cayunus/EE464-TermProject/Cayunus/Calculations/RmsOfTrapezoid&Triangular.pdf

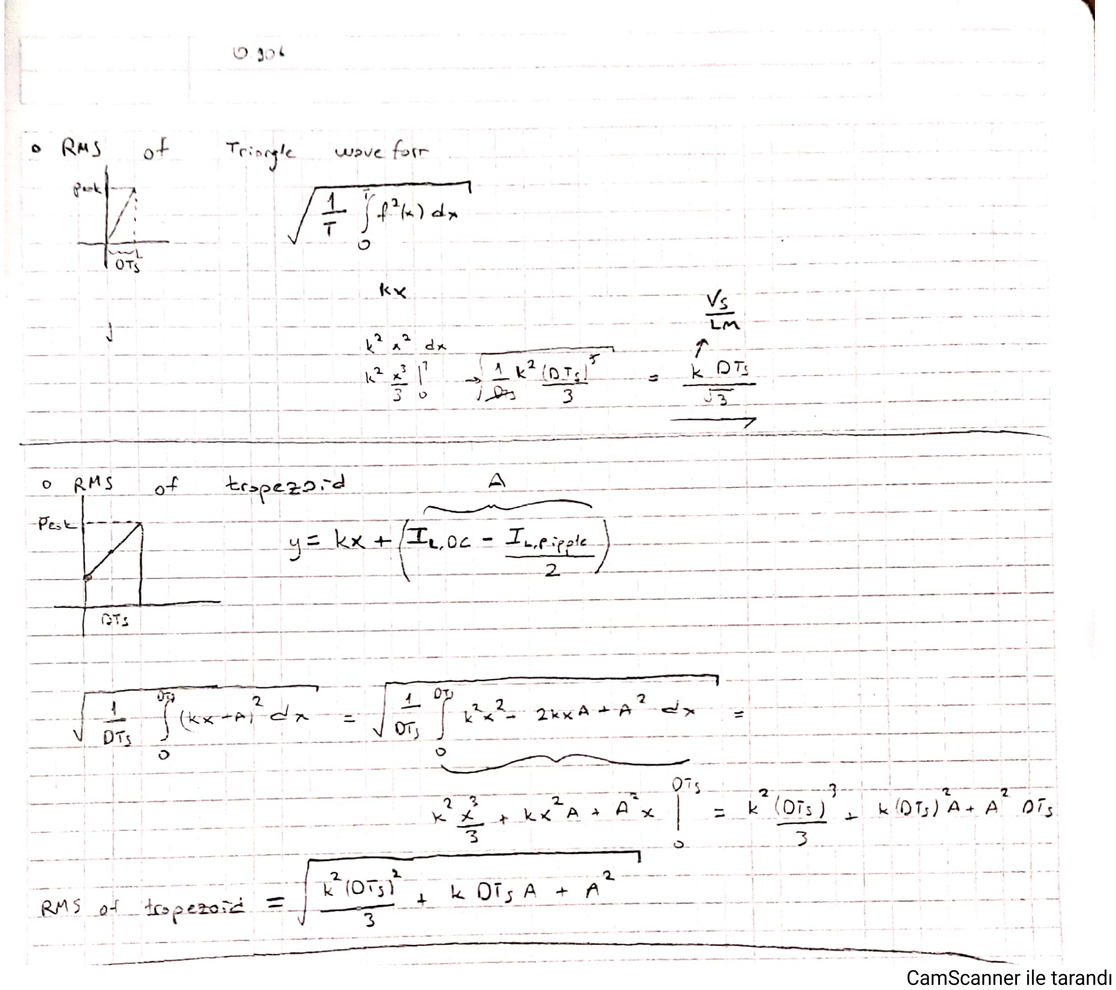
[picture p64: page 1]
