cayunus/EE464-TermProject/PCB/EE464_PCB_Yunus/Downloaded_Sym_Foot/ETD34/User Library-ETD34.STEP

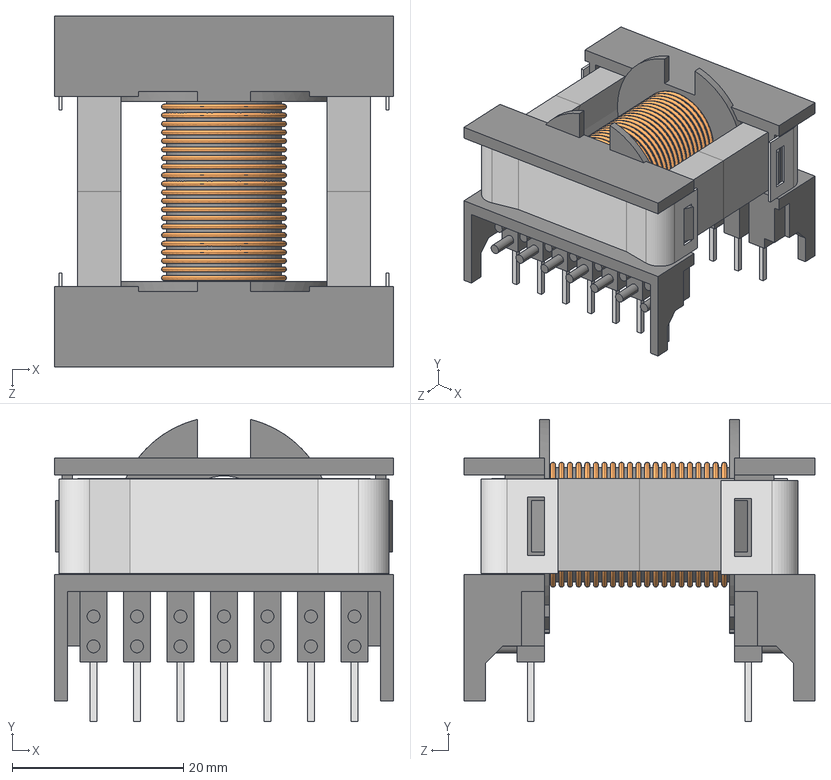
[picture p80: CAD file, 2021-06-09]
PCB/EE464_PCB_Yunus/Downloaded_Sym_Foot/ETD34/User Library-ETD34.STEP
39.6 x 35.3 x 41.0 mm
ETD34_Part3 x 2
ETD34_Part4
CPH-ETD34-1S-14P
ETD34_Part2 x 2
