cayunus/EE464-TermProject/PCB/EE464_PCB_Yunus/Downloaded_Sym_Foot/LT8316IFE_UltraLib/AltiumDesigner/2021-05-20_21-10-27/TSSOP_20_ADI.step

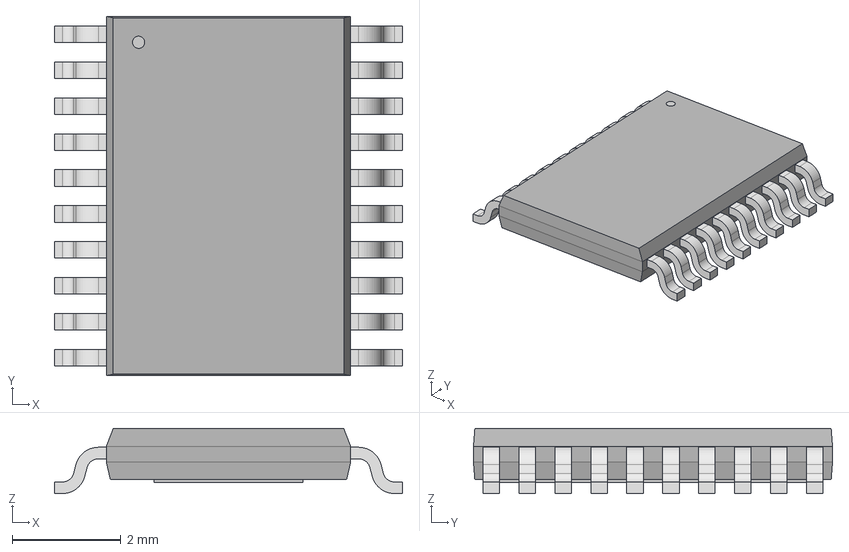
[picture p81: CAD file, 2021-05-27]
PCB/EE464_PCB_Yunus/Downloaded_Sym_Foot/LT8316IFE_UltraLib/AltiumDesigner/2021-05-20_21-10-27/TSSOP_20_ADI.step
6.40 x 6.60 x 1.20 mm
