cayunus/EE464-TermProject/PCB/EE464_PCB_Yunus/Downloaded_Sym_Foot/R0603/User Library-CR1608-0603.step

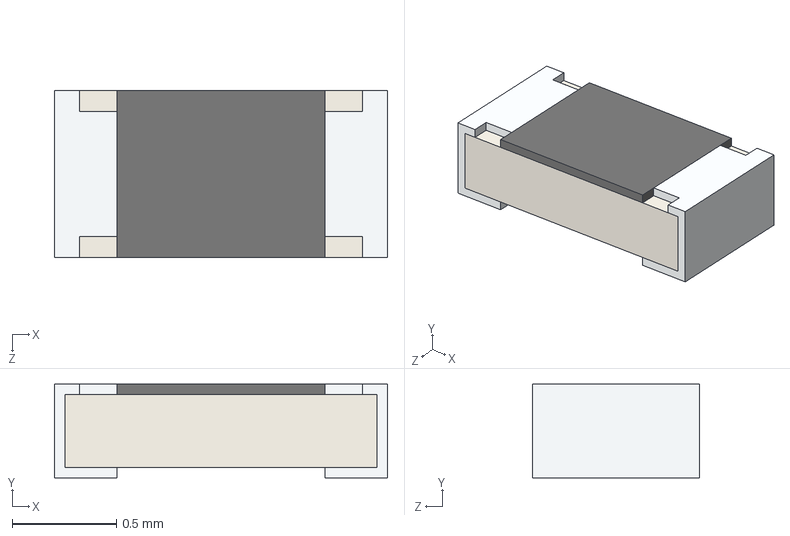
[picture p82: CAD file, 2021-05-27]
PCB/EE464_PCB_Yunus/Downloaded_Sym_Foot/R0603/User Library-CR1608-0603.step
1.60 x 0.45 x 0.8 mm
