cayunus/EE464-TermProject/PCB/EE464_PCB_Yunus/Downloaded_Sym_Foot/Rsense1220/AltiumDesigner/2021-05-21_21-18-42/RES_1220_SUS.step

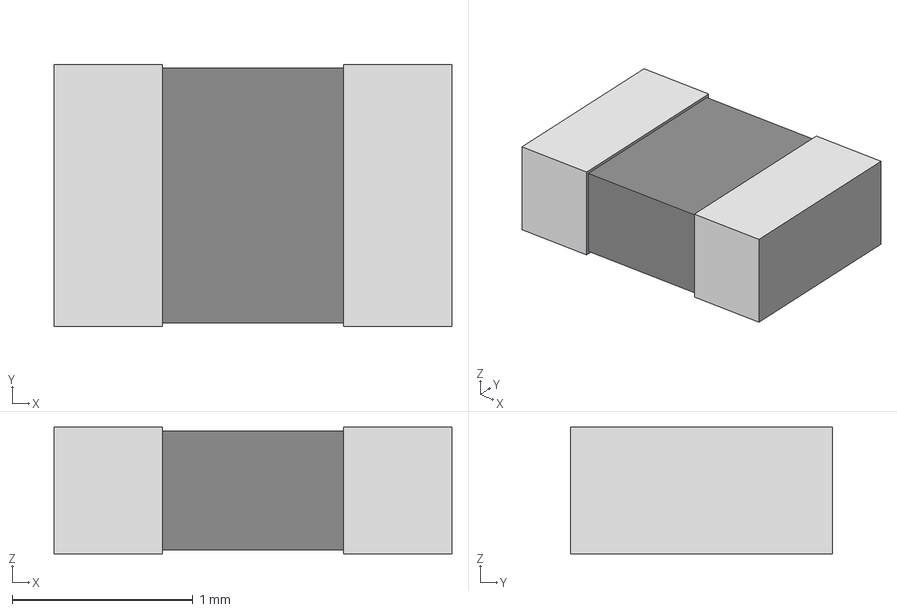
[picture p83: CAD file, 2021-05-27]
PCB/EE464_PCB_Yunus/Downloaded_Sym_Foot/Rsense1220/AltiumDesigner/2021-05-21_21-18-42/RES_1220_SUS.step
2.20 x 1.45 x 0.7 mm
