cayunus/EE464-TermProject/PCB/EE464_PCB_Yunus/Downloaded_Sym_Foot/SOD128/User Library-SOD128.step

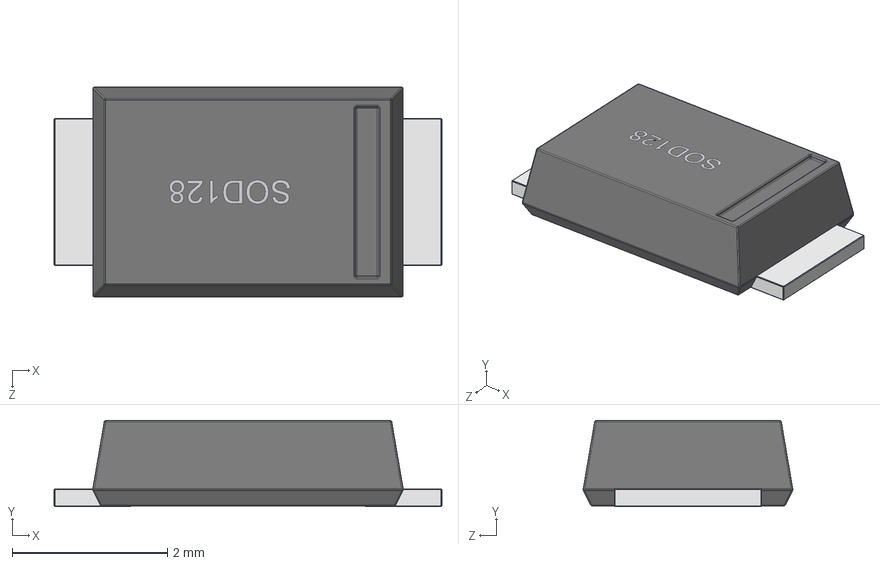
[picture p84: CAD file, 2021-06-09]
PCB/EE464_PCB_Yunus/Downloaded_Sym_Foot/SOD128/User Library-SOD128.step
5.00 x 1.11 x 2.70 mm
