cayunus/EE464-TermProject/PCB/EE464_PCB_Yunus/Downloaded_Sym_Foot/TO220-AB/stps20h100ct.stp

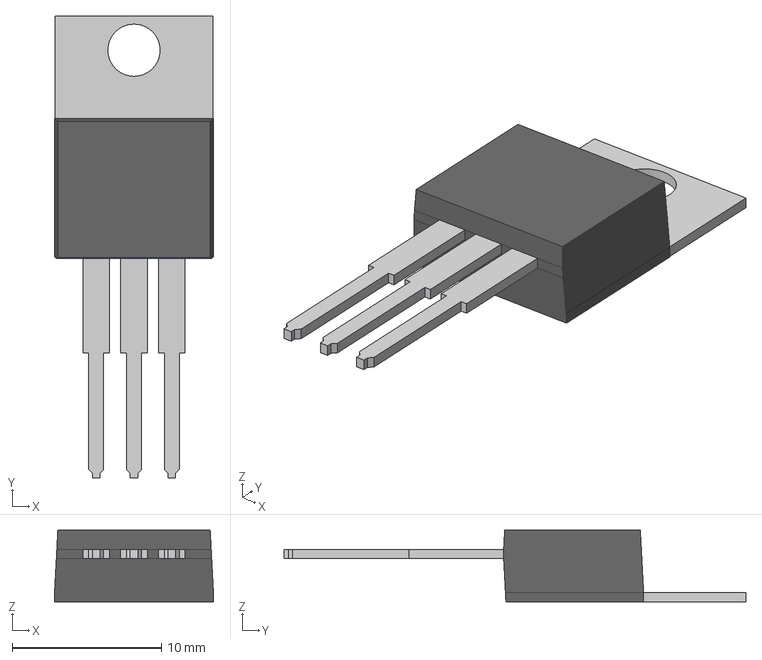
[picture p85: CAD file, 2021-06-09]
PCB/EE464_PCB_Yunus/Downloaded_Sym_Foot/TO220-AB/stps20h100ct.stp
10.7 x 31.0 x 4.83 mm
