cayunus/EE464-TermProject/PCB PDF/Flyback_PCB.pdf

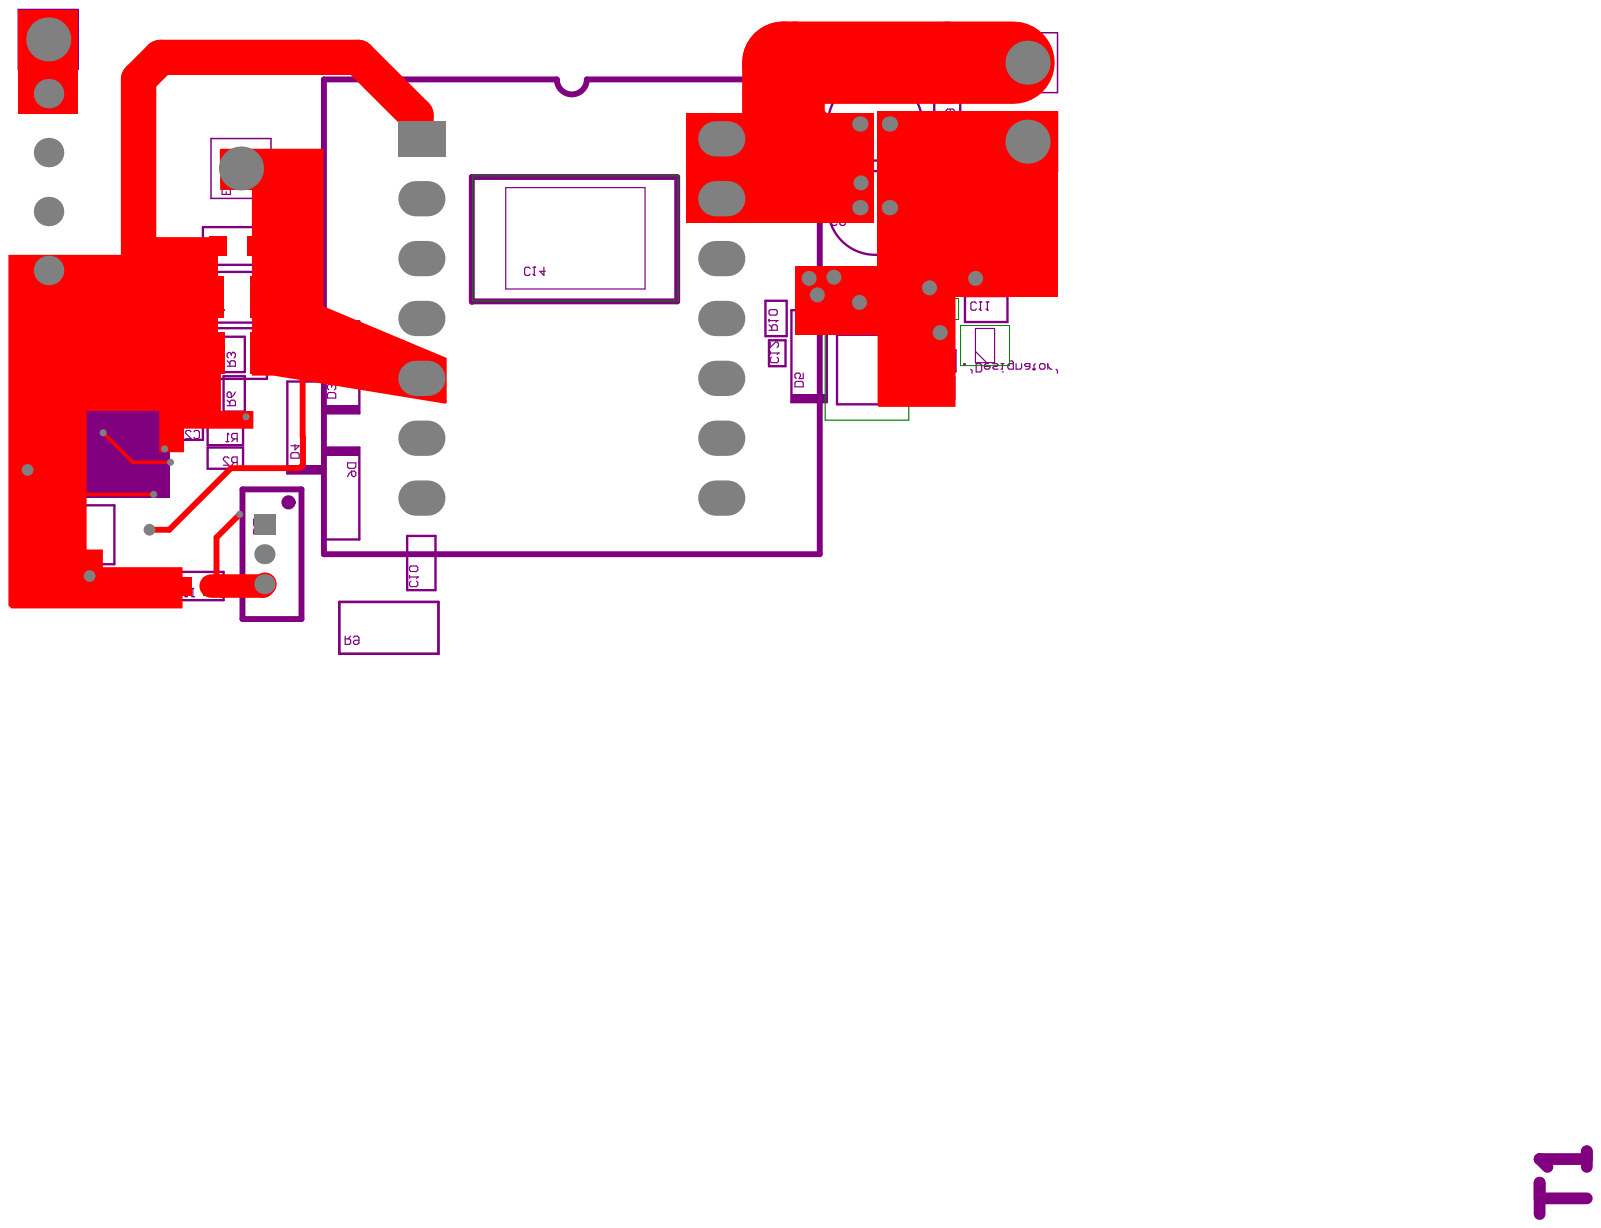
[picture p86: page 1]

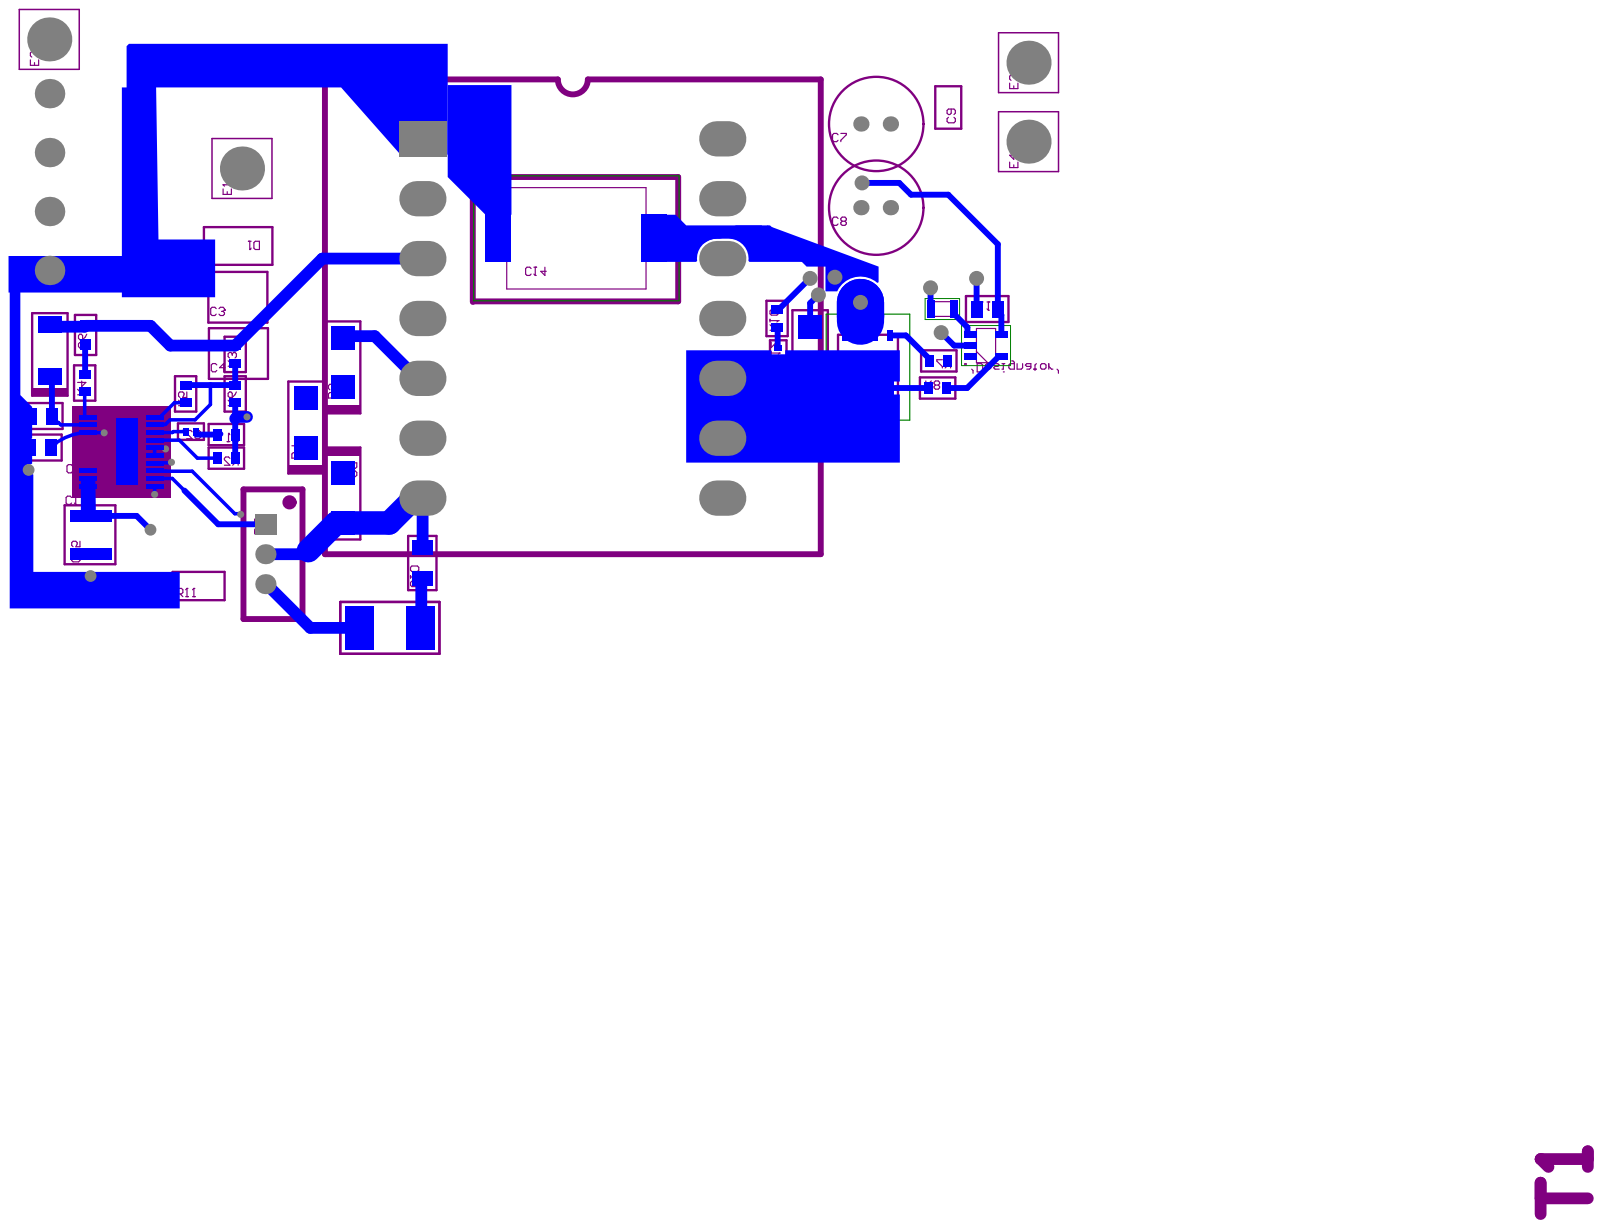
[picture p87: page 2]

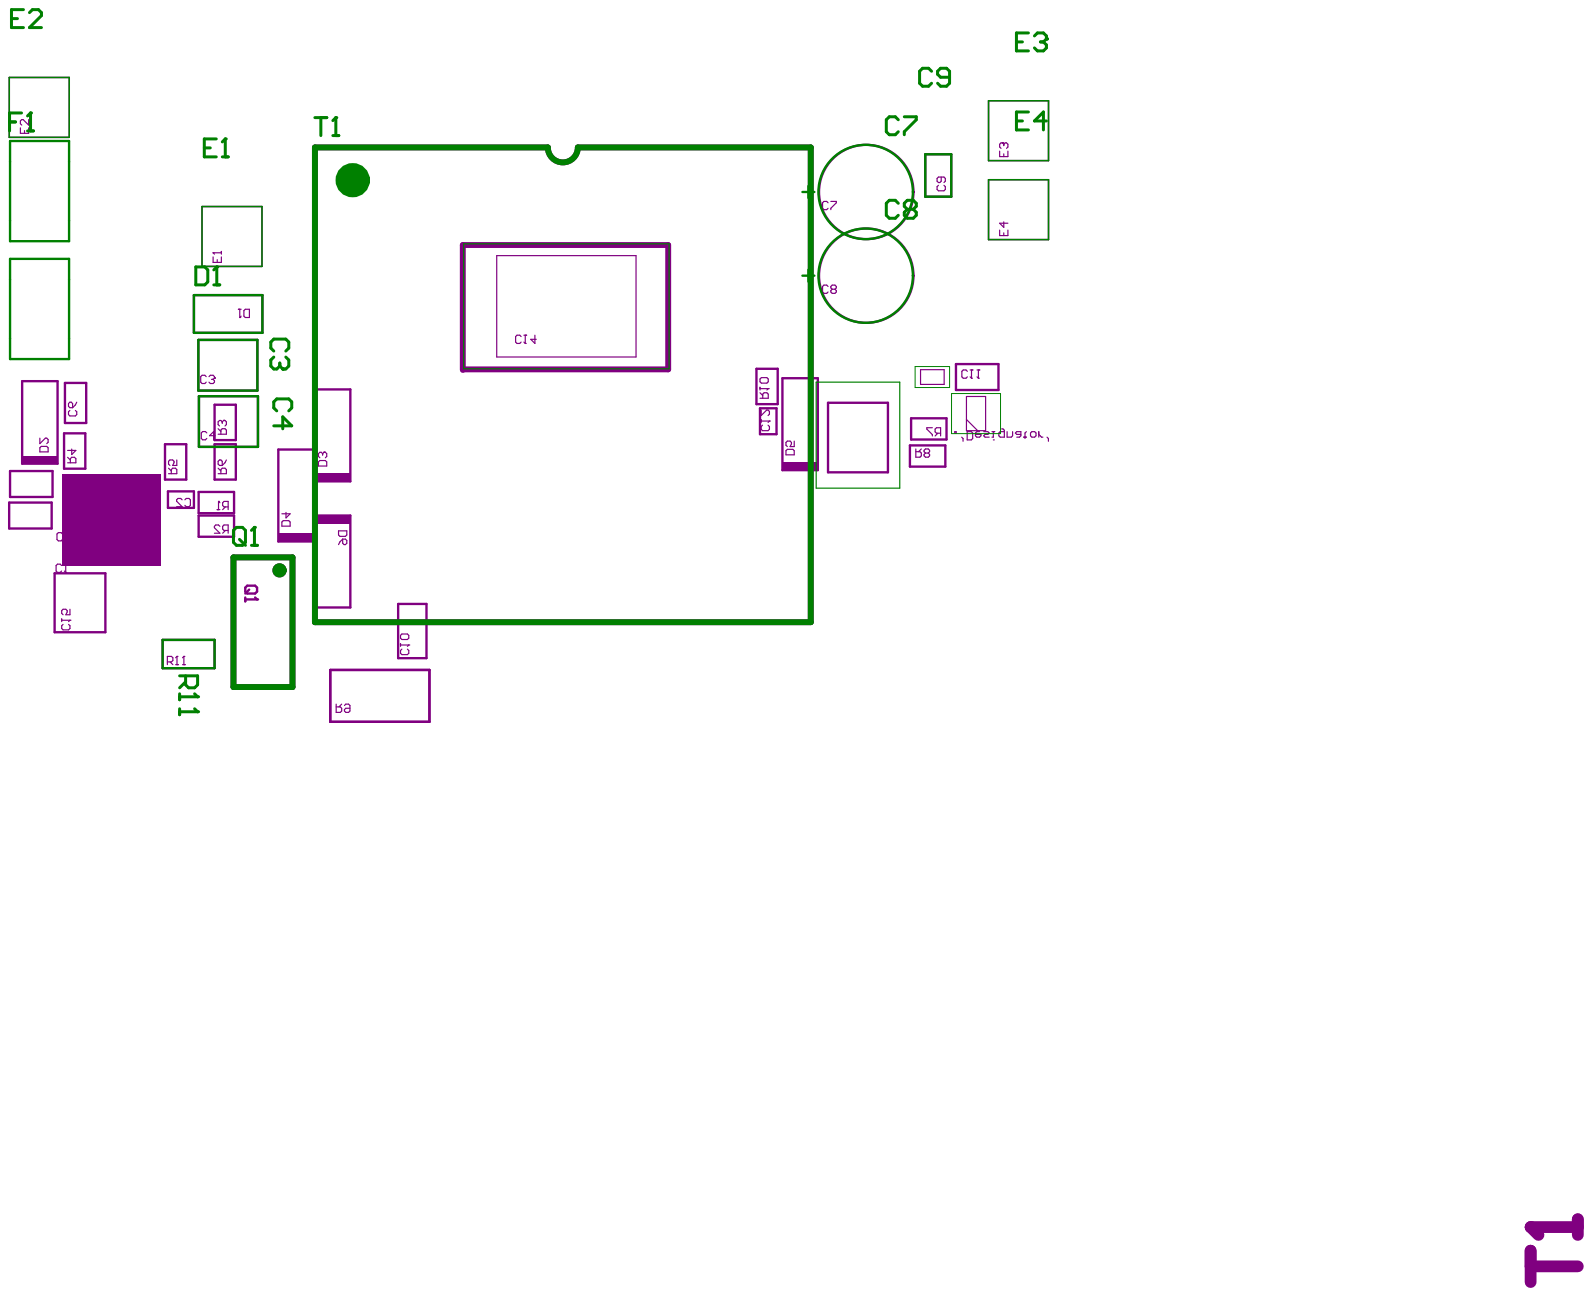
[picture p88: page 3]

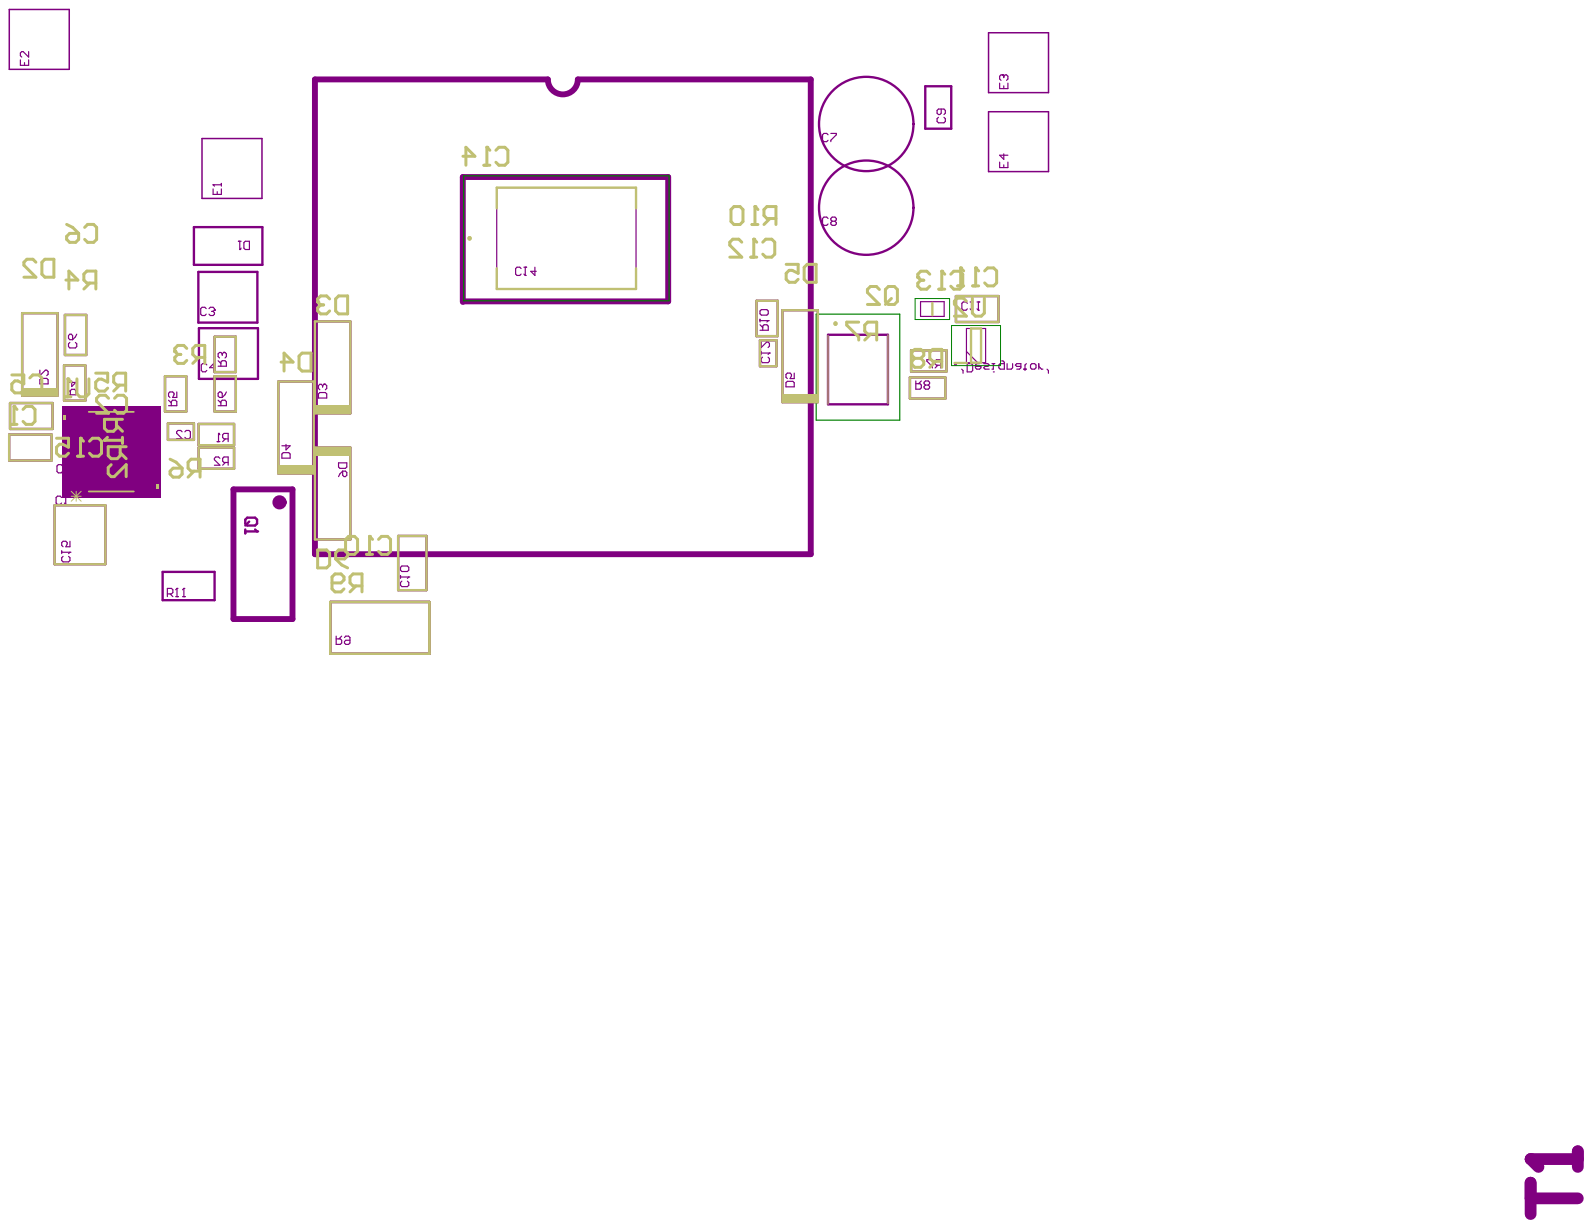
[picture p89: page 4]

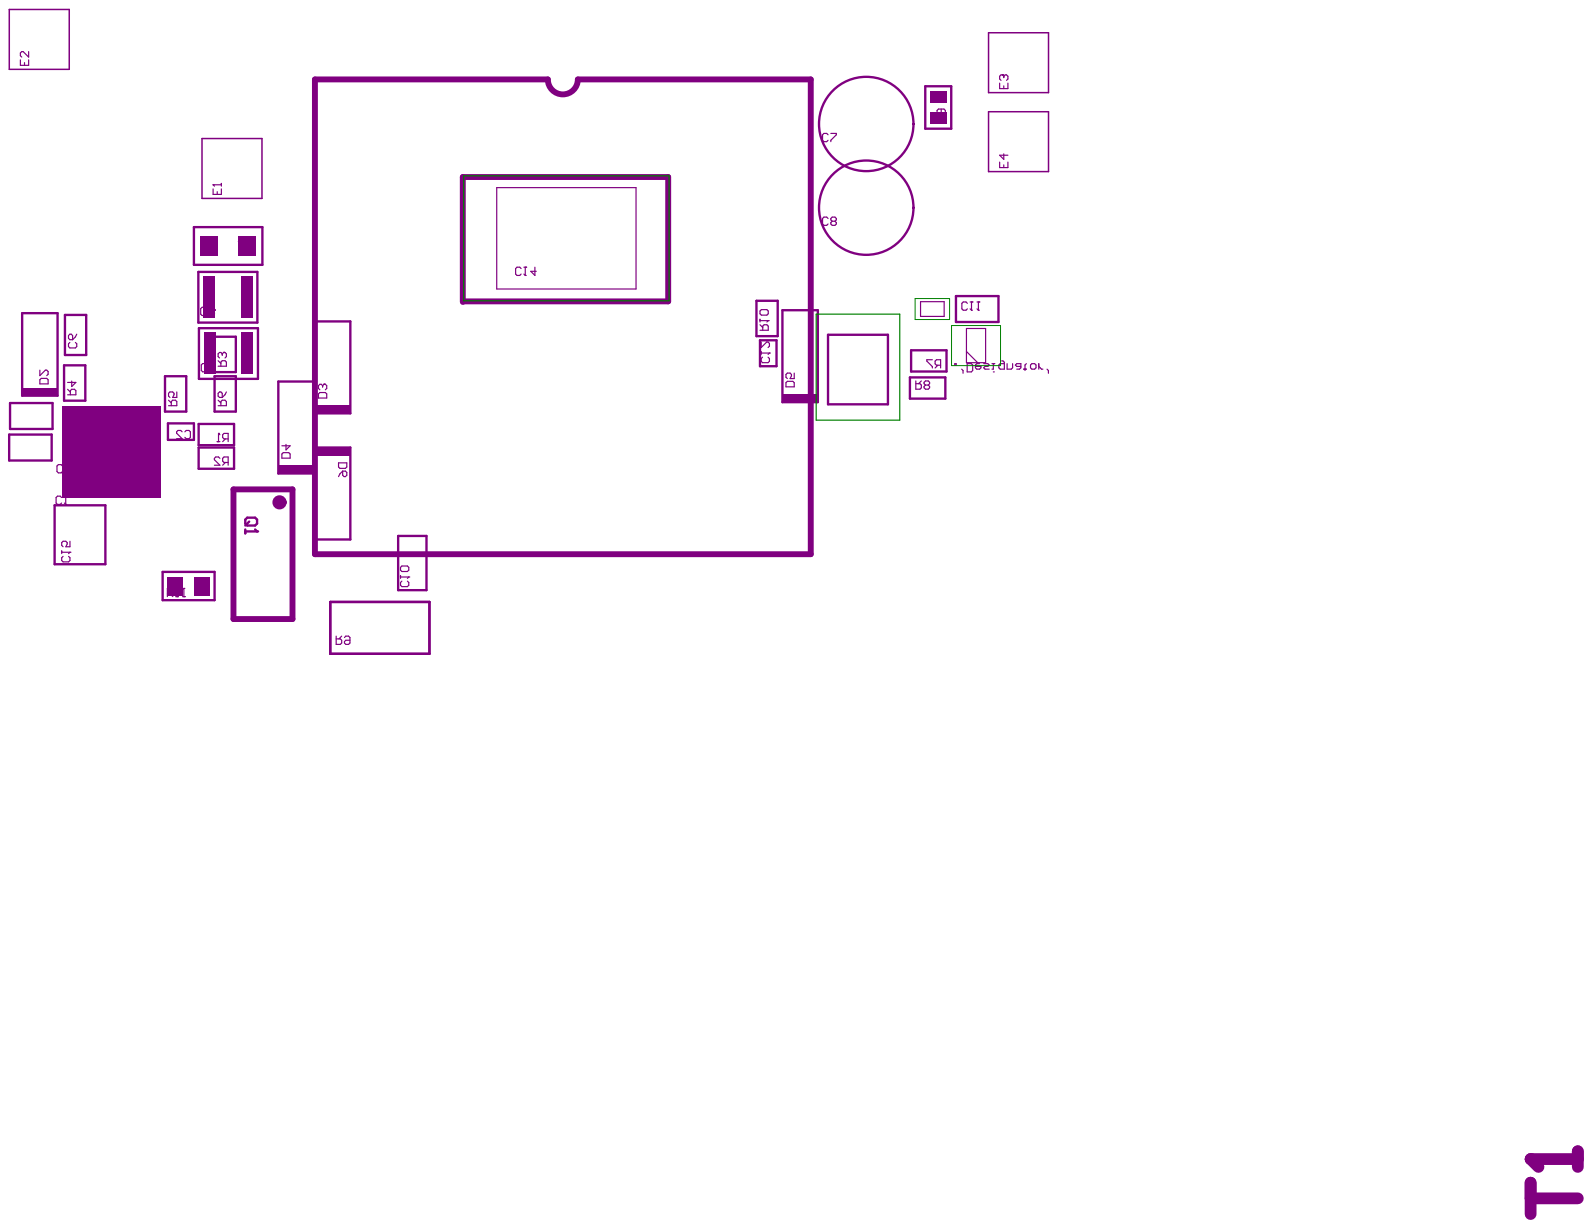
[picture p90: page 5]

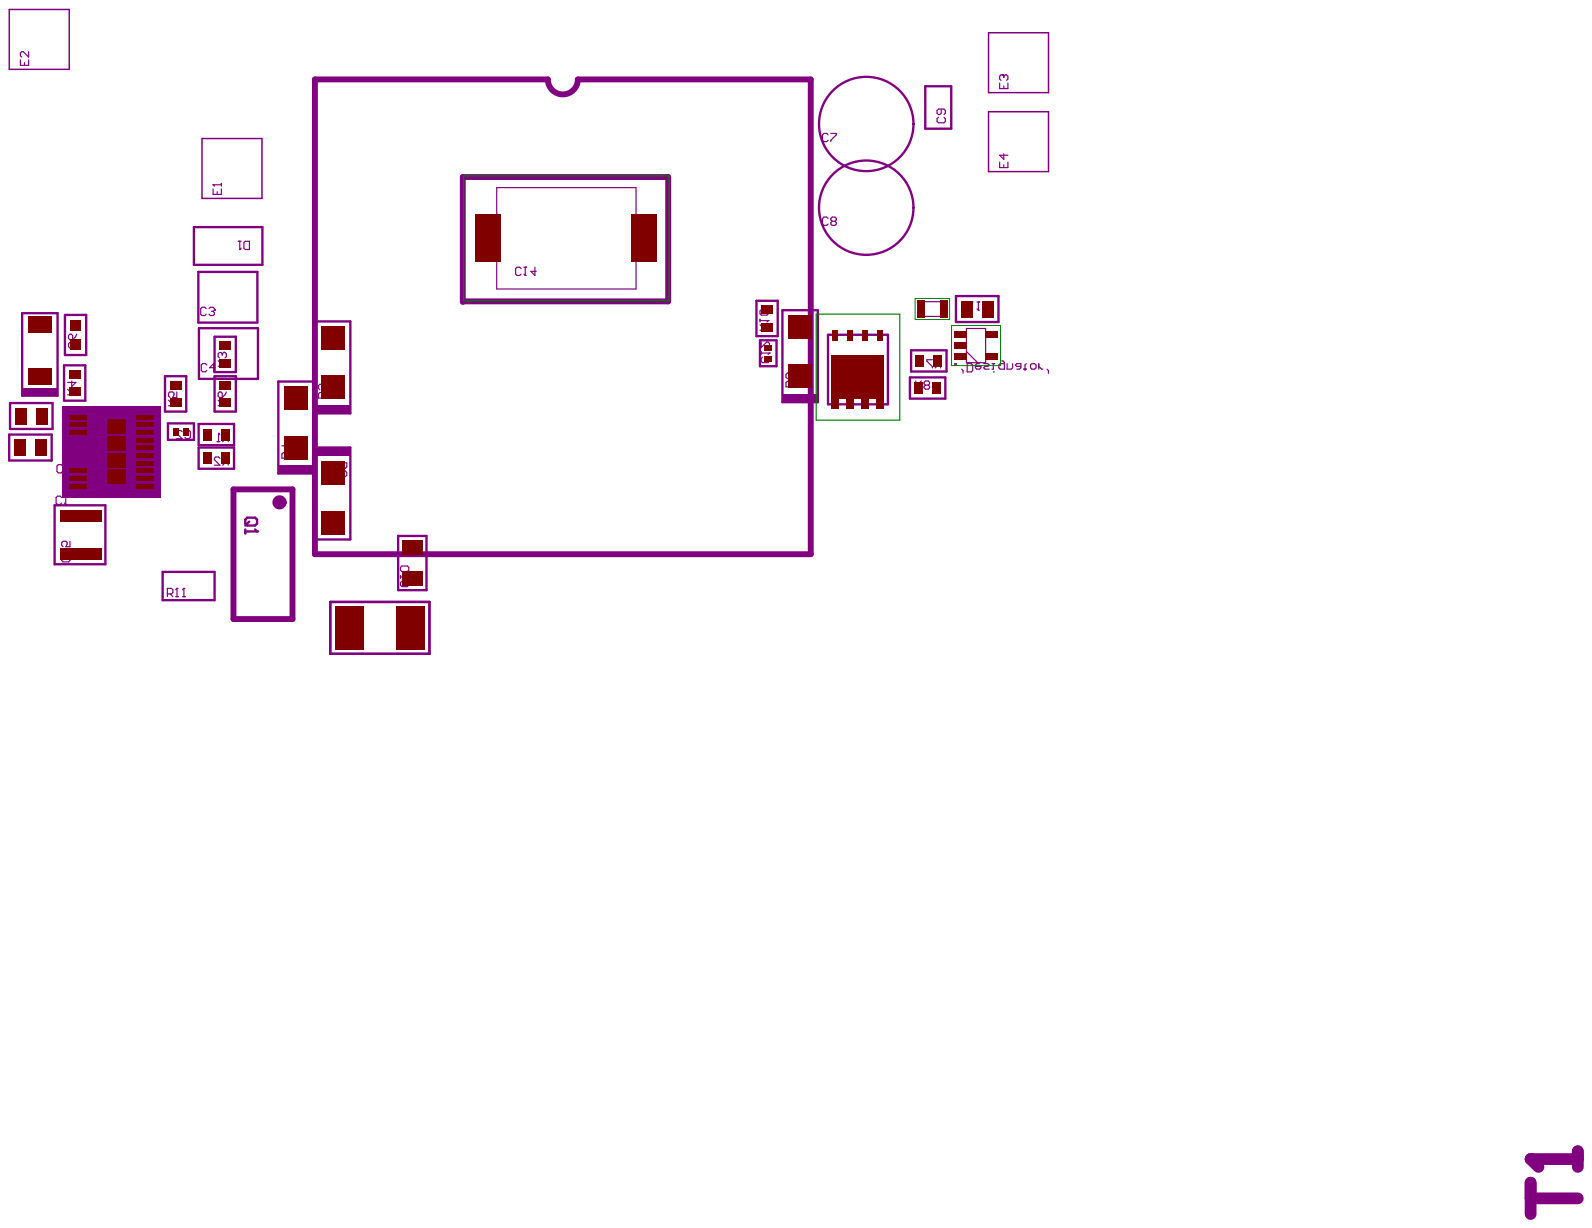
[picture p91: page 6]

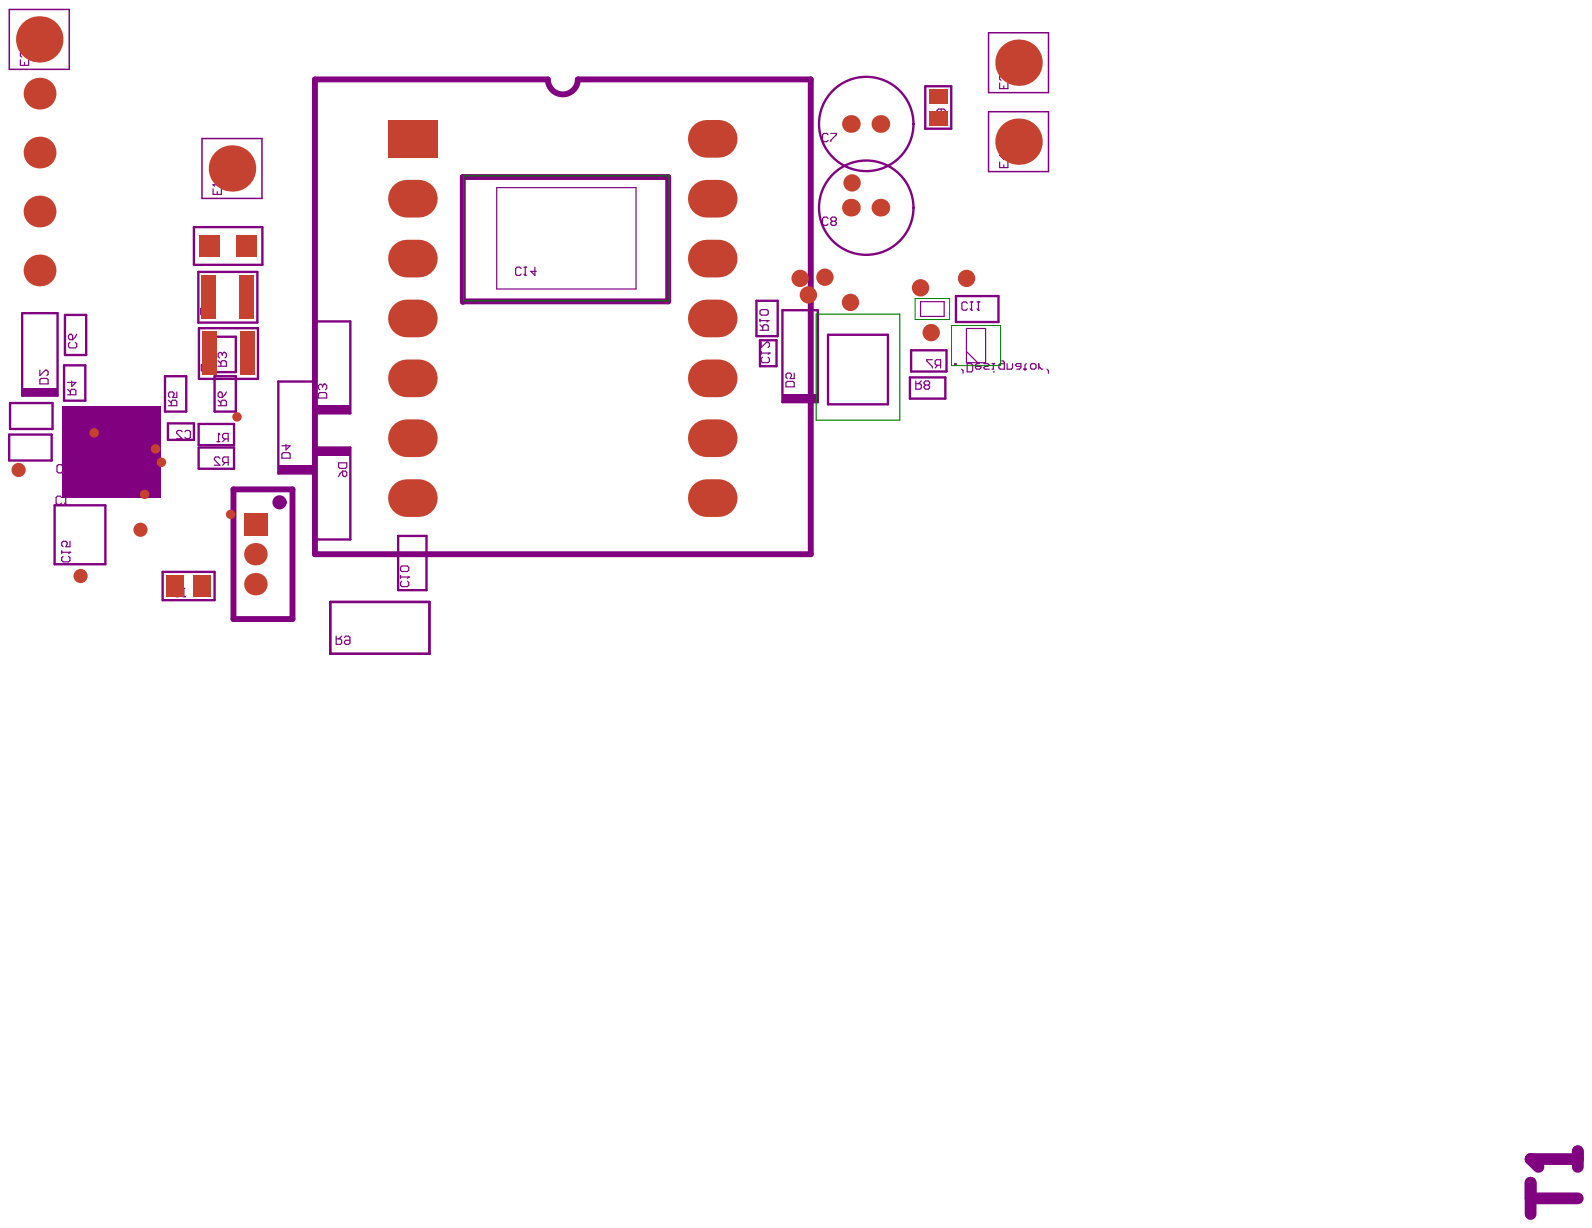
[picture p92: page 7]

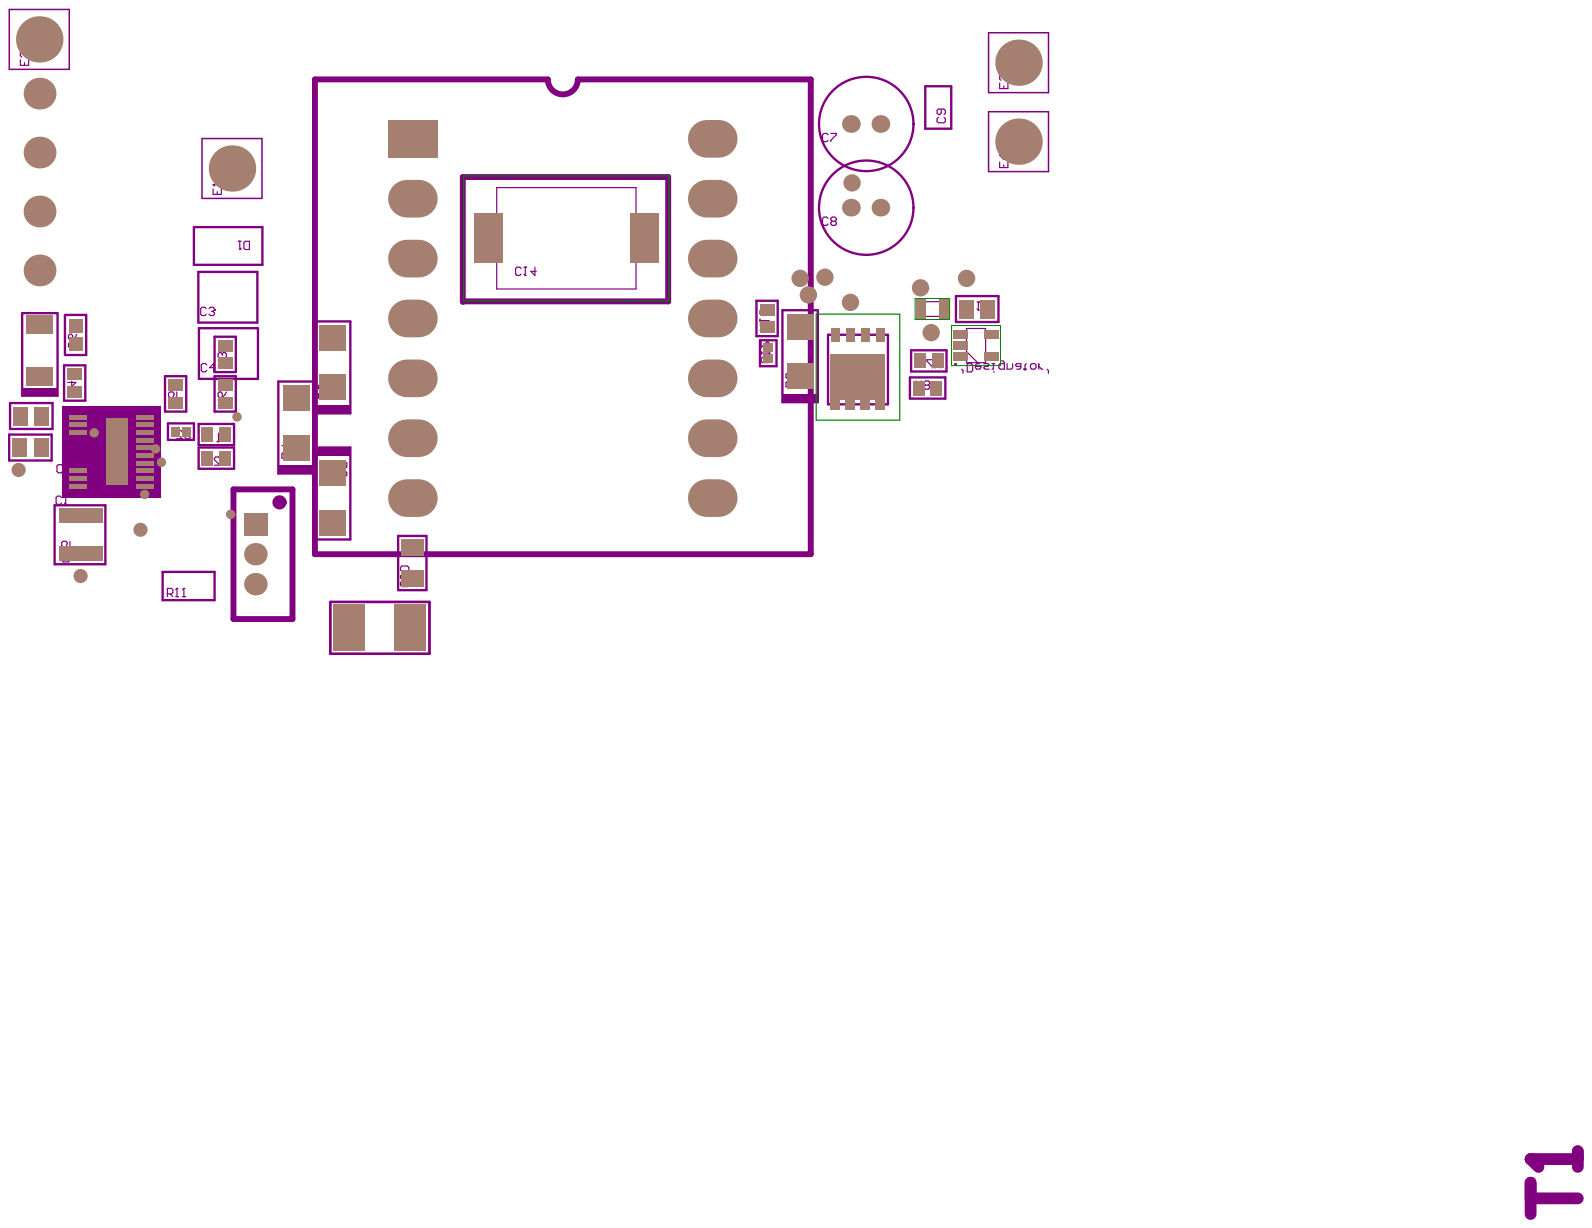
[picture p93: page 8]

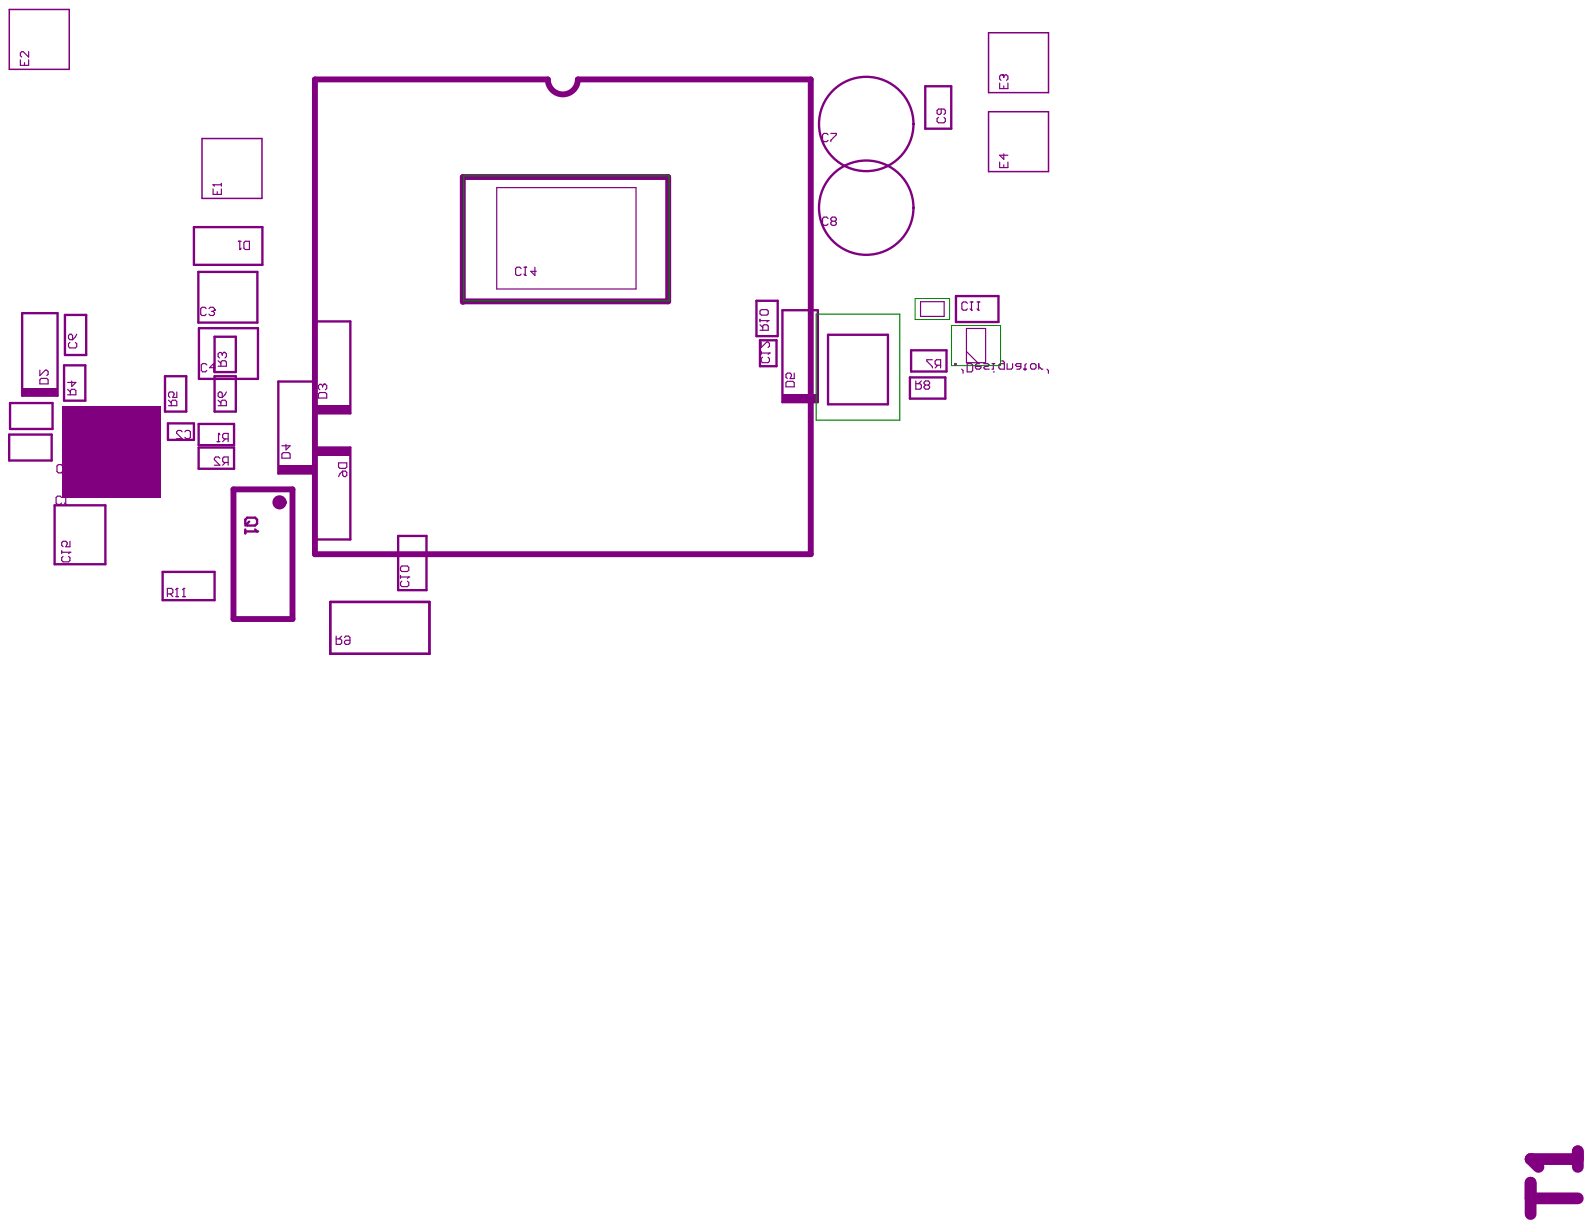
[picture p94: page 9]

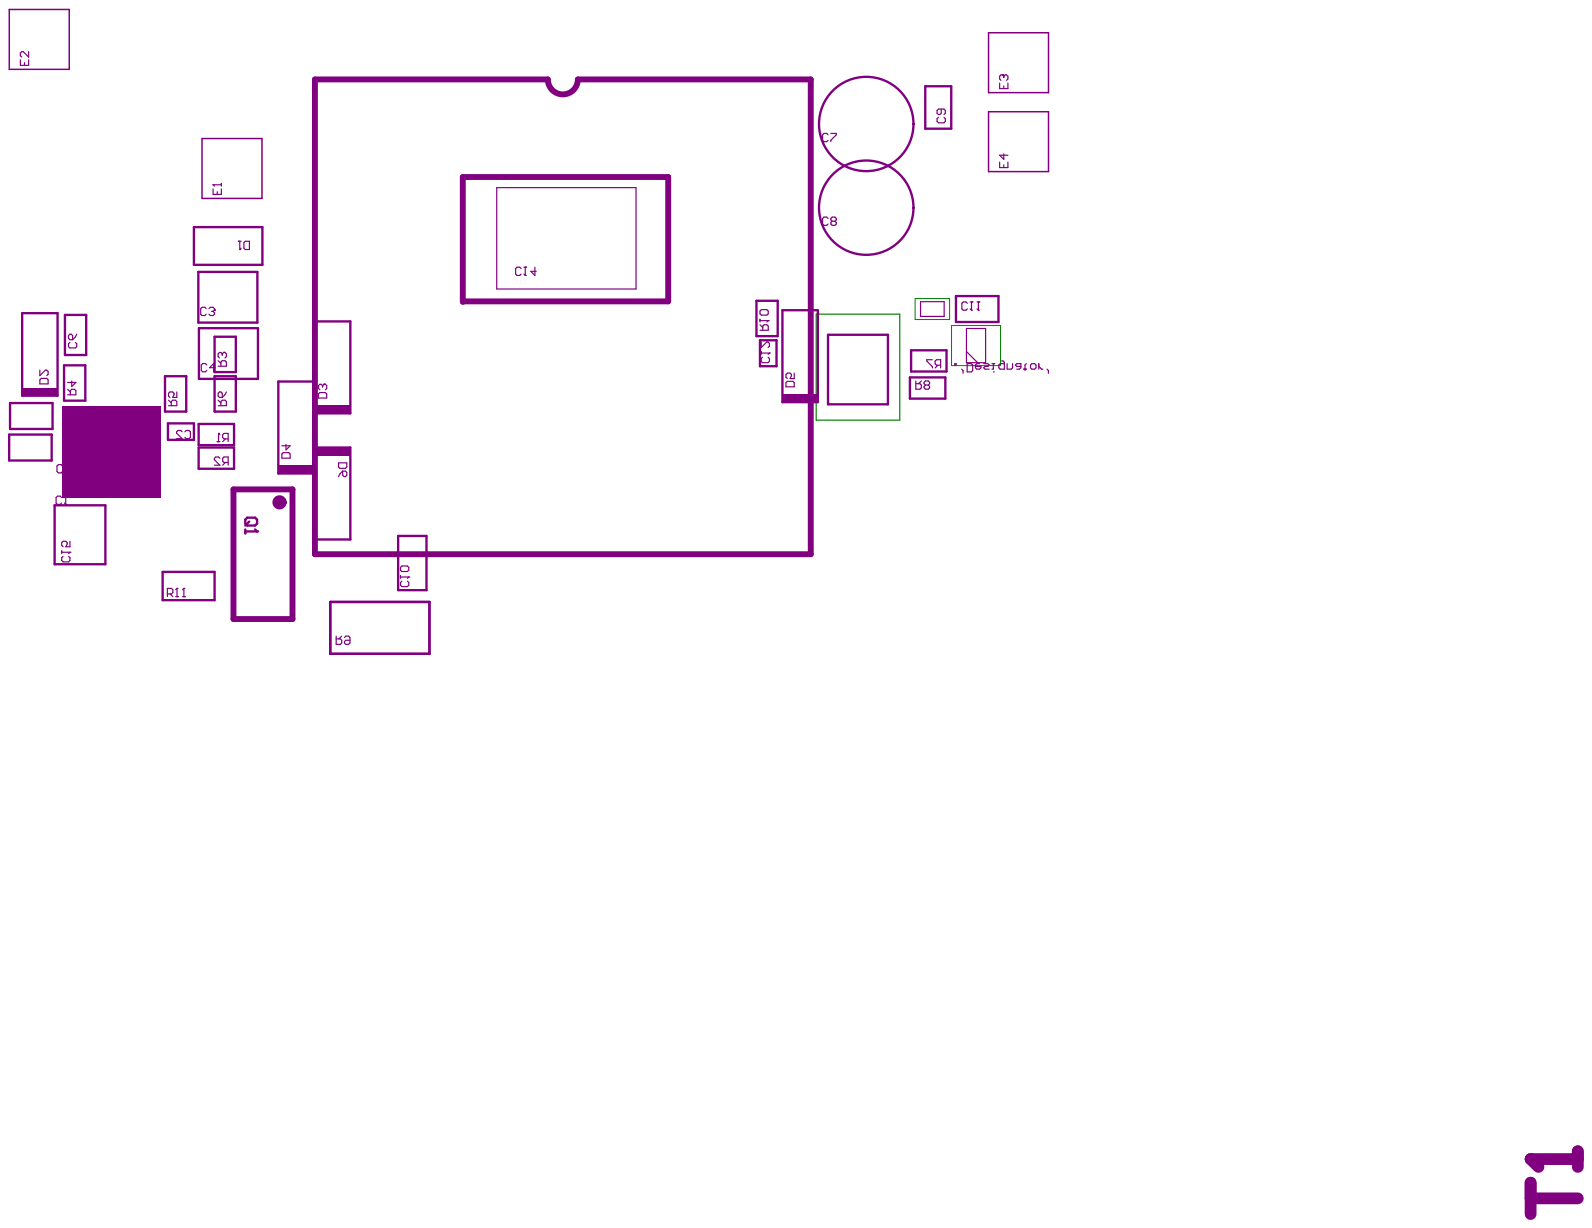
[picture p95: page 13]

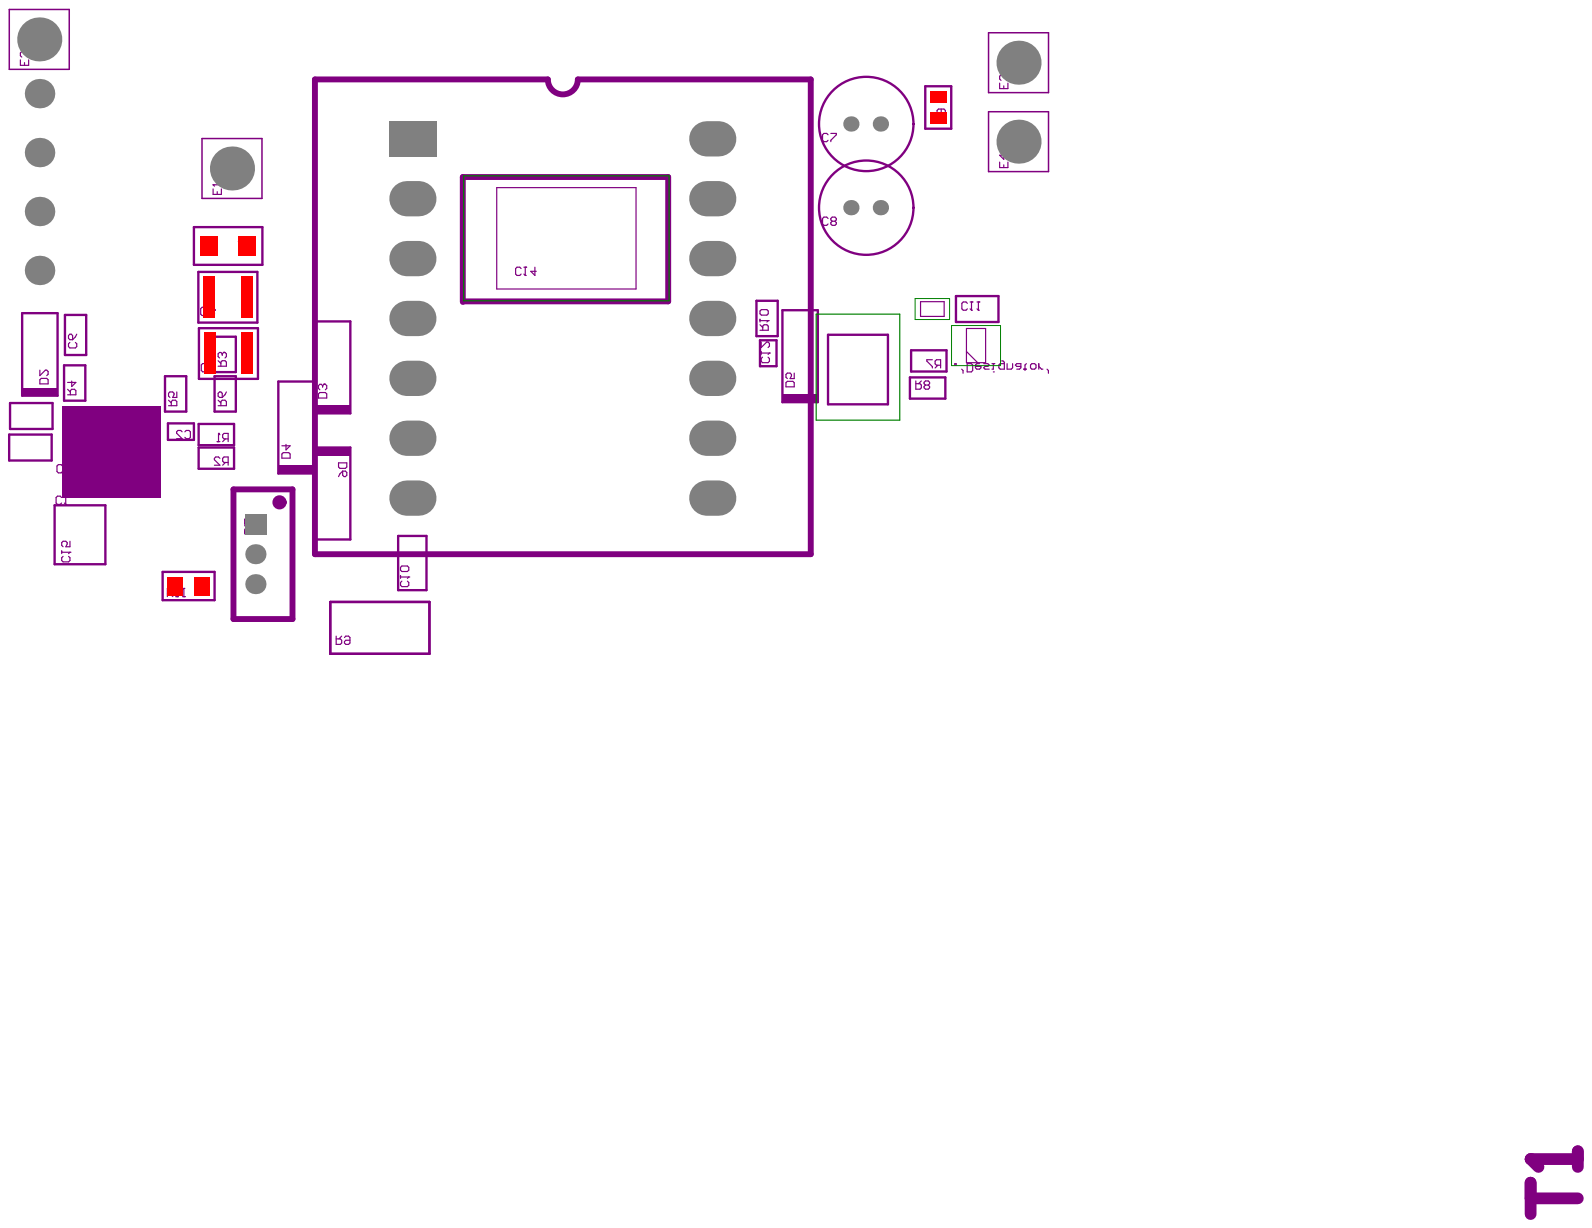
[picture p96: page 14]

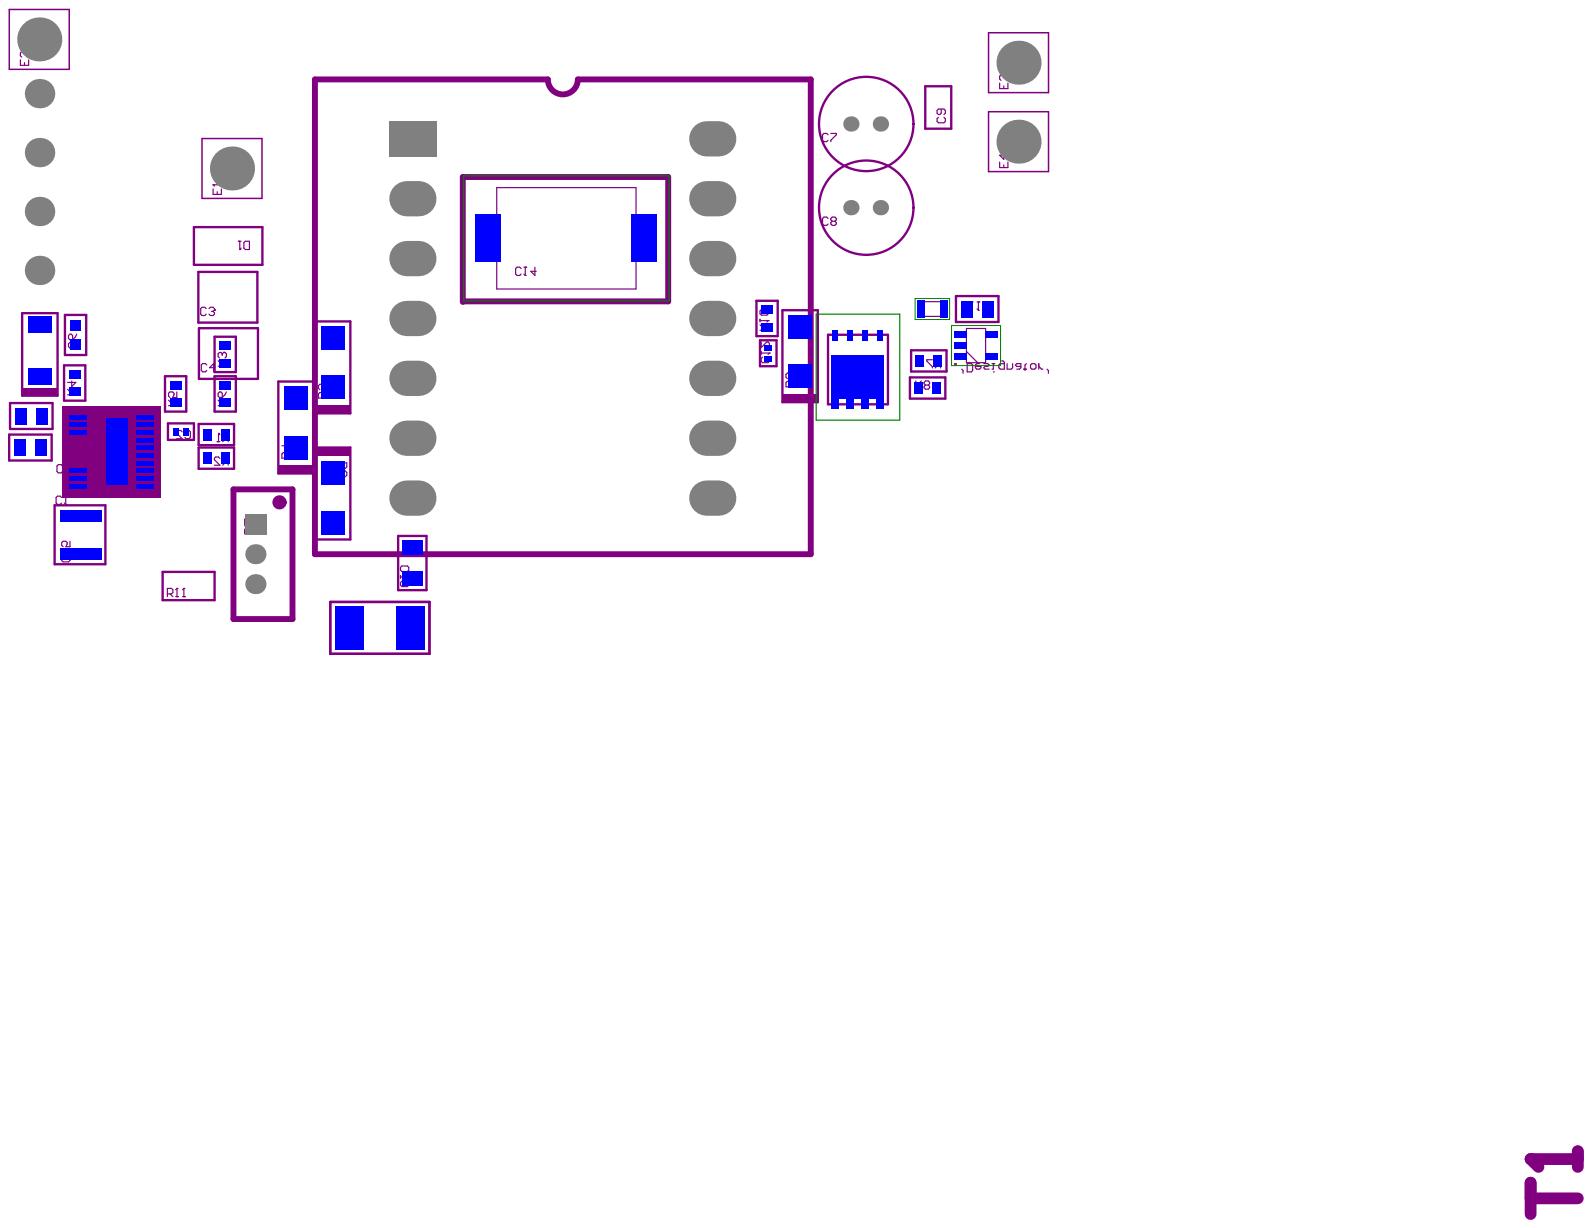
[picture p97: page 15]

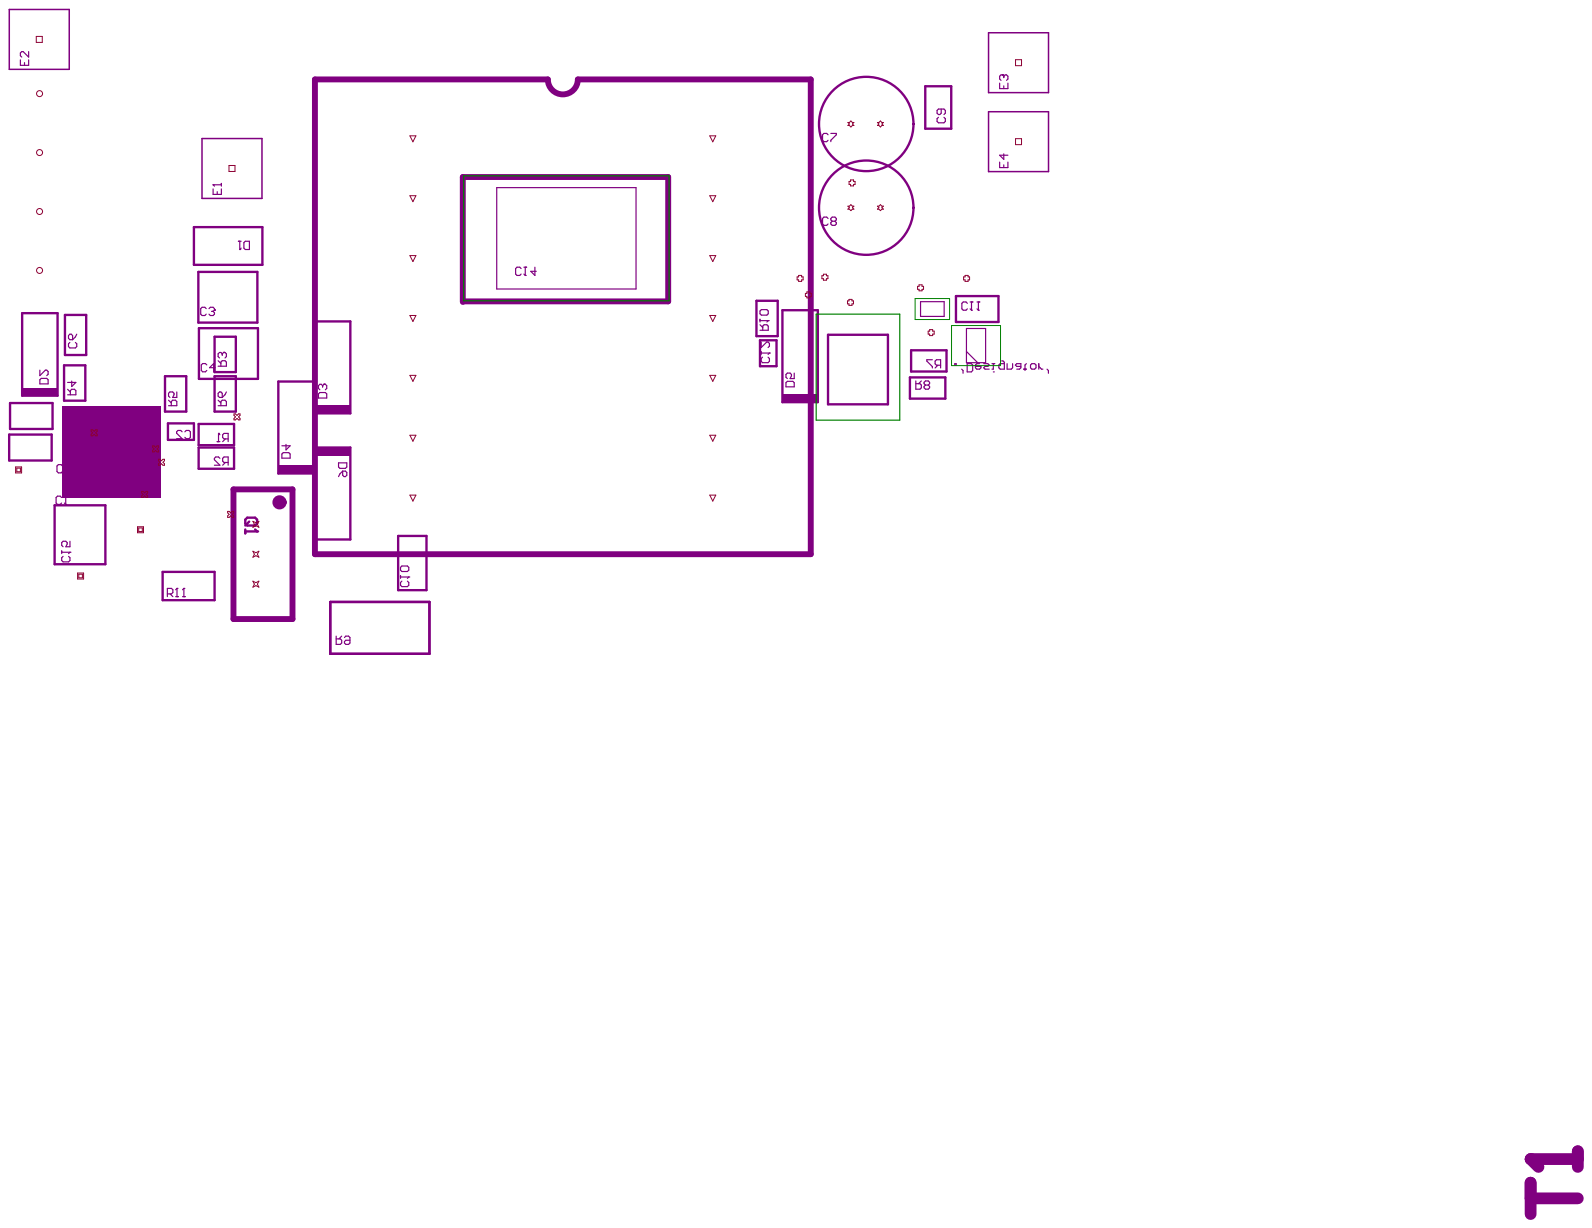
[picture p98: page 16]

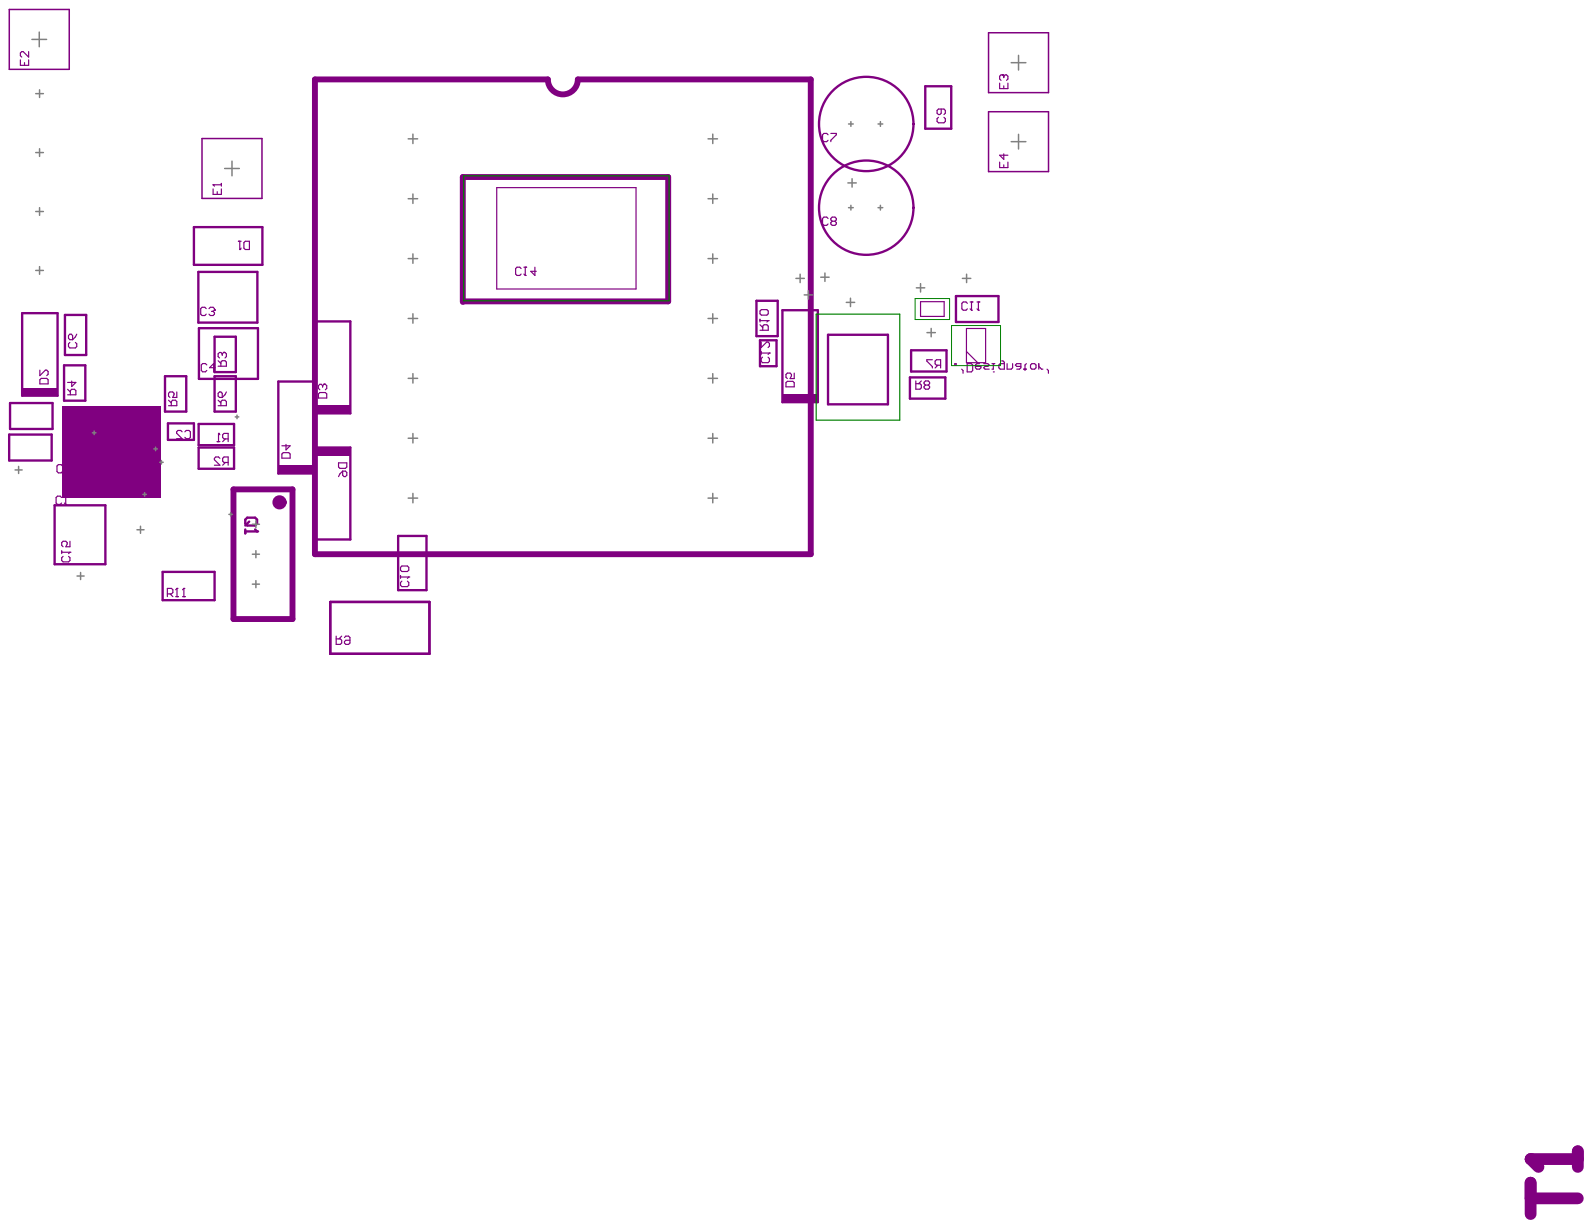
[picture p99: page 17]
