cayunus/EE464-TermProject/HalidF/LTSpiceTestModels/3805simple.asc

C1: cap; 560µ; V=50 Rser=23m
C2: cap; 50p
C3: cap; .047µ
C4: cap; 0.022µ
C5: cap; 10µ; Rser=10m
C6: cap; 10µ; Rser=10m
C7: cap; 250p
C8: cap; 2.2µ
D1: schottky; RB228T100
D2: zener; 1N5385B
D3: diode; RFN1L7S
D4: zener; TFZ10B
L1: ind2; 540µ; Rser=24m
L2: ind2; 8.44µ; Rser=17m
L3: ind; 5.4µ
Q1: npn
R1: res; 3.01k
R2: res; 200
R3: res; 380k
R4: res; 27k
R5: res; 56K
R6: res; 20m
R7: res; 25
R8: res; 118K
R9: res; 20k
R10: res; 2Meg
Rload: res; 1.44
U1: LTC3805
U2: IPA70R600P7S_L0
V2: voltage; 400
Named nets: 0, IN, OUT
K1 L1 L2 1
Frequency Resistor
Soft Start Capacitor
INPUT
220v - 400V
OUTPUT
12V 100W
.tran 40m steady startup
.model 1N5385B D(IS=1.54e-17 N=1 XTI=1 Rs=.1 Cjo=10p TT=10n BV=170 IBV=8m NBV=50 Vpk=170 mfg=OnSemi type=Zener)
