cayunus/EE464-TermProject/HalidF/LTSpiceTestModels/4430isolated.asc

C1: cap; 4.7µ
C2: polcap; 100µ; Rser=0.1
C3: cap; .05µ
C4: cap; .001µ
C5: cap; .1µ
D1: schottky; MBRS1100
D2: diode; 1N4148
L1: ind2; 200µ; Rser=0.344
L2: ind2; 200µ; Rser=0.344
Q1: nmos; FDS6680A
R1: res; 399
R2: res; 1000
R3: res; 0.2
R4: res; 5.1K
R5: res; 73.2K
R6: res; 10K
R7: res; 475K
R8: res; 3K
R9: res; 200K
R10: res; 4.99K
Rload: res; 100
U1: LTC3803
U2: MOC207
U3: LT4430
V1: voltage; 13
V2: voltage; 5
Named nets: 0, OUT, IN
K1 L1 L2 1
.tran 7m startup
