cayunus/EE464-TermProject/HalidF/LTSpiceTestModels/8311.asc

C1: cap; .015µ
C2: cap; 22µ; x2; Rser=10m
C3: cap; 4.7µ
C4: cap; 4.7µ
C5: cap; 68p
C6: cap; 220p
C7: cap; 2200p; Rser=3.7K Cpar=68p
C8: cap; .01µ
C9: cap; .01µ
C10: polcap; 470µ; V=16 Irms=825m Rser=0.084 Lser=0 mfg="United Chemi-Con" pn="LXF16VB471M10X16LL" type="Al electrolytic"
C11: cap; 15n
C12: cap; 100n
C13: cap; 3.5n; Rser=25K Cpar=50p
C14: cap; 2.2µ
C15: cap; 2.2µ
C16: cap; 1µ
D1: schottky; BAT46WJ
D2: schottky; BAT46WJ
D3: schottky; BAT46WJ
D4: schottky; MBRS1100
L1: ind2; 216µ; Rser=12m Rpar=5k
L2: ind2; 216µ; Rser=4.5m
L3: ind2; 6.8µ; Rser=5m Rpar=10K
L4: ind2; 785µ; Rser=.6
L5: ind2; 785µ; Rser=.6
L6: ind2; 222µ; Rser=1.6
L7: ind2; 25.66µ; Rser=.65
L8: ind2; 25.66µ; Rser=.45
M1: nmos; BSC077N12NS3
M2: nmos; BSC082N10LS
M3: nmos; BSC082N10LS
M4: pmos; Si7113DN
M5: nmos; Si7802DN
R1: res; 5m
R2: res; 100K
R3: res; 11.3K
R4: res; 5.9K
R5: res; 1.82K
R6: res; 100k
R7: res; 3.16K
R8: res; 100
R9: res; 1K
R10: res; 499K
R11: res; 100
R12: res; 560
R13: res; 31.6K
R14: res; 71.5K
R15: res; 34K
R16: res; 49.9K
R17: res; 22.6K
R18: res; 7.32K
R19: res; 2K
R20: res; 10K
R21: res; .15
R22: res; 499
R23: res; 1.1K
R24: res; 10K
R25: res; 100K
R26: res; 100K
R27: res; 100
Rload1: res; 1.2
U1: LT8311
U3: PC817D
U5: LT3752
V1: voltage; 30
Named nets: 0, IN, OUT, Vaux, INTVcc
K1 L1 L2 1
.tran 5.5m startup
K2 L5 L4 1
K3 L6 L7 L8 1
