cayunus/EE464-TermProject/8316synch.asc

C1: cap; 4.7µ
C2: cap; 470p
C3: cap; 47p; Rser=10K
C4: cap; 100p
C5: cap; 4.7µ
C6: cap; 4.7µ
C7: cap; 10µ; Rser=5m Lser=1n
C8: cap; 470µ; N=2; Rser=20m Lser=5n
C9: cap; 100n; Rser=20K
C10: cap; 1µ
D1: zener; 1N5375B
D3: schottky; RB058L150
D4: diode; RFN1L7S
D5: zener; 1N5378B; N=2
L1: ind2; 480µ; Rser=0.15
L2: ind2; 7.5µ; Rser=0.0025 Cpar=0.5p
L3: ind2; 7.5µ; Rser=0.3
L4: ind; 4.8µ
R1: res; 500
R2: res; 50
R4: res; 108K
R5: res; 48k
R6: res; 5.25k
R7: res; 2.3k
R8: res; 4.7
R9: res; 60k
Rload: res; 1.44
Rsense: res; 20m
U1: LT8316
U2: IPA70R600P7S_L0
U3: LT8309
U5: BSC040N10NS5_L0
V1: voltage; 220
Named nets: IN, OUT, 0
K1 L1 L2 L3 1
8:1:1
.tran 0 20m 0.6m
Primary 220-400V
Secondary 12V
