cayunus/EE464-TermProject/Stability/Stability Analysis Model.asc

C1: cap; 4.7µ
C3: cap; 47p; Rser=10K
C4: cap; 100p
C5: cap; 4.7µ
C6: cap; 470p
C7: cap; 10µ; Rser=5m Lser=1n
C8: cap; 470µ; N=2; Rser=20m Lser=5n
C9: cap; 100n; Rser=20k
D3: schottky; RB058L150
D4: diode; RFN1L7S
D5: zener; 1N5378B; N=2
L1: ind2; 400µ; Rser=0.25
L2: ind2; 6.25µ; Rser=0.003 Cpar=0.5p
L3: ind2; 6.25µ; Rser=0.3
L4: ind; 4µ
R1: res; 500
R2: res; 50
R3: res; 10
R4: res; 108k
R5: res; 48k
R6: res; 5.3k
R9: res; 60k
Rload: res; 1.44
Rsense: res; 20m
U1: LT8316
U2: IPA70R600P7S_L0
U3: STPS20SM120STN
V1: voltage; 220
V2: voltage; SINE(0 10m {Freq})
Named nets: 0, IN, OUT, A, B
K1 L1 L2 L3 1
8:1:1
STABILITY ANALYSIS MODEL
.measure Aavg avg V(a)
.measure Bavg avg V(b)
.measure Are avg (V(a)-Aavg)*cos(360*time*Freq)
.measure Aim avg -(V(a)-Aavg)*sin(360*time*Freq)
.measure Bre avg (V(b)-Bavg)*cos(360*time*Freq)
.measure Bim avg -(V(b)-Bavg)*sin(360*time*Freq)
.measure GainMag param 20*log10(hypot(Are,Aim) / hypot(Bre,Bim))
.measure GainPhi param mod(atan2(Aim, Are) - atan2(Bim, Bre)+180,360)-180
.param t0=7m
.tran 0 {t0+25/freq} {t0}
.step oct param freq 10k 80k 10
.save V(a) V(b)
.option plotwinsize=0 numdgt=15
